loopj/gc-nano-jewel/firmware/src/AnimatedGIF_LittleFS.cpp

#include <LittleFS.h>

#include "AnimatedGIF_LittleFS.h"

static File f;

void *GIFOpenFile(const char *fname, int32_t *pSize)
{
  f = LittleFS.open(fname, "r");
  if (f) {
    *pSize = f.size();
    return (void *)&f;
  }
  return NULL;
}

void GIFCloseFile(void *pHandle)
{
  File *f = static_cast<File *>(pHandle);
  if (f != NULL)
    f->close();
}

int32_t GIFReadFile(GIFFILE *pFile, uint8_t *pBuf, int32_t iLen)
{
  int32_t iBytesRead;
  iBytesRead = iLen;
  File *f    = static_cast<File *>(pFile->fHandle);
  // Note: If you read a file all the way to the last byte, seek() stops working
  if ((pFile->iSize - pFile->iPos) < iLen)
    iBytesRead = pFile->iSize - pFile->iPos - 1; // <-- ugly work-around
  if (iBytesRead <= 0)
    return 0;
  iBytesRead  = (int32_t)f->read(pBuf, iBytesRead);
  pFile->iPos = f->position();
  return iBytesRead;
}

int32_t GIFSeekFile(GIFFILE *pFile, int32_t iPosition)
{
  int i   = micros();
  File *f = static_cast<File *>(pFile->fHandle);
  f->seek(iPosition);
  pFile->iPos = (int32_t)f->position();
  i           = micros() - i;
  return pFile->iPos;
}
