loopj/gc-nano-jewel/firmware/src/AnimatedGIF_LittleFS.h

#include <AnimatedGIF.h>

void *GIFOpenFile(const char *fname, int32_t *pSize);
void GIFCloseFile(void *pHandle);
int32_t GIFReadFile(GIFFILE *pFile, uint8_t *pBuf, int32_t iLen);
int32_t GIFSeekFile(GIFFILE *pFile, int32_t iPosition);
